JaneDoe649/PicoPAC/Kicad/PicoPAC.kicad_sch

## KiCad design Kicad/PicoPAC.kicad_sch (2024-10-13)

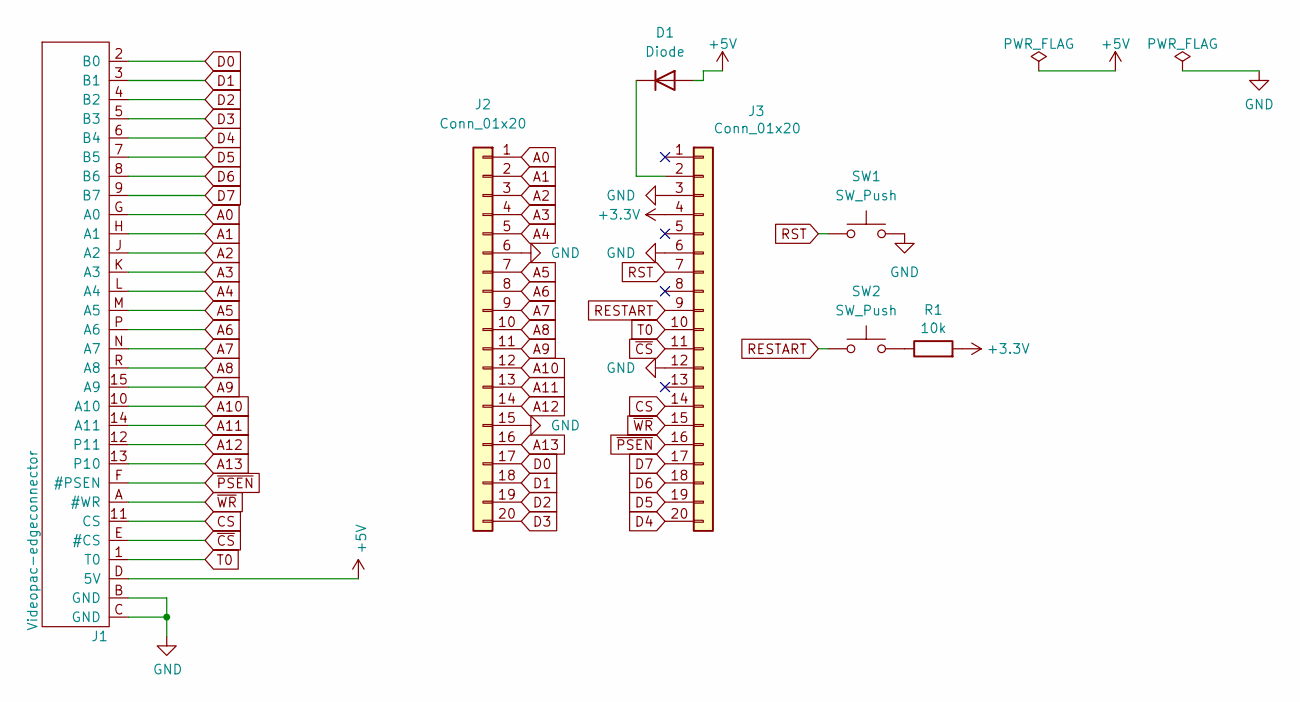
[picture p2: schematic PicoPAC.kicad_sch]

Parts:
D1: Diode; D_DO-35_SOD27_P7.62mm_Horizontal
J1: Videopac-edgeconnector; videopac-edgecon
J2, J3: Conn_01x20; PinSocket_1x20_P2.54mm_Vertical
R1: 10k; R_Axial_DIN0207_L6.3mm_D2.5mm_P7.62mm_Horizontal
SW1, SW2: SW_Push; SW_PUSH_6mm

Connections:
+3.3V: J3.4, R1.2
+5V: D1.2 (A), J1.D (5V)
A0: J1.G (A0), J2.1
A1: J1.H (A1), J2.2
A2: J1.J (A2), J2.3
A3: J1.K (A3), J2.4
A4: J1.L (A4), J2.5
A5: J1.M (A5), J2.7
A6: J1.P (A6), J2.8
A7: J1.N (A7), J2.9
A8: J1.R (A8), J2.10
A9: J1.15 (A9), J2.11
A10: J1.10 (A10), J2.12
A11: J1.14 (A11), J2.13
A12: J1.12 (P11), J2.14
A13: J1.13 (P10), J2.16
CS: J1.11 (CS), J3.14
D0: J1.2 (B0), J2.17
D1: J1.3 (B1), J2.18
D2: J1.4 (B2), J2.19
D3: J1.5 (B3), J2.20
D4: J1.6 (B4), J3.20
D5: J1.7 (B5), J3.19
D6: J1.8 (B6), J3.18
D7: J1.9 (B7), J3.17
GND: J1.B (GND), J1.C (GND), J2.6, J2.15, J3.3, J3.6, J3.12, SW1.2
unnamed: D1.1 (K), J3.2
unnamed: R1.1, SW2.2
RESTART: J3.9, SW2.1
RST: J3.7, SW1.1
T0: J1.1 (T0), J3.10
~CS: J1.E (#CS), J3.11
~PSEN: J1.F (#PSEN), J3.16
~WR: J1.A (#WR), J3.15
