JaneDoe649/PicoPAC/VSC-PicoPAC/selectgame.h

unsigned char __attribute__((aligned(4)))  selectgame[] = {0x44, 0xc3, 0x04, 0x09, 0x93, 0x00, 0x84, 0x0c, 0x84, 0x28, 0x04, 0x44, 0xa5, 0xb5, 0xb9, 0xa2, 0x81, 0xb8, 0x3f, 0x04, 0x30, 0x15, 0x99, 0xfe, 0x94, 0x28, 0x89, 0x03, 0x99, 0xfd, 0x94, 0x28, 0x99, 0xfc, 0x94, 0x28, 0x89, 0x03, 0x05, 0x83, 0xb9, 0x36, 0xf1, 0xd3, 0x12, 0x96, 0x32, 0xb4, 0x00, 0x83, 0xf1, 0xd3, 0x13, 0x96, 0x3a, 0xd4, 0x00, 0x83, 0xf1, 0xd3, 0x14, 0x96, 0x42, 0xf4, 0x00, 0x83, 0xf1, 0xd3, 0x15, 0x96, 0x4b, 0xf5, 0x14, 0x00, 0x83, 0xf1, 0xd3, 0x16, 0x96, 0x54, 0xf5, 0x34, 0x00, 0x83, 0xf1, 0xd3, 0x17, 0x96, 0x5d, 0xf5, 0x54, 0x00, 0x83, 0xf1, 0xd3, 0x18, 0x96, 0x66, 0xf5, 0x74, 0x00, 0x83, 0x83, 0xb8, 0x32, 0xb0, 0x01, 0x18, 0xb0, 0x23, 0x18, 0xb0, 0x45, 0x18, 0xb0, 0x67, 0x83, 0xfd, 0xe7, 0xe7, 0xad, 0x83, 0x94, 0x75, 0x91, 0x83, 0xff, 0xff, 0xff, 0xff, 0xff, 0xff, 0xff, 0xff, 0xff, 0xff, 0xff, 0xff, 0xff, 0xff, 0xff, 0xff, 0xff, 0xff, 0xff, 0xff, 0xff, 0xff, 0xff, 0xff, 0xff, 0xff, 0xff, 0xff, 0xff, 0xff, 0xff, 0xff, 0xff, 0xff, 0xff, 0xff, 0xff, 0xff, 0xff, 0xff, 0xff, 0xff, 0xff, 0xff, 0xff, 0xff, 0xff, 0xff, 0xff, 0xff, 0xff, 0xff, 0xff, 0xff, 0xff, 0xff, 0xff, 0xff, 0xff, 0xff, 0xff, 0xff, 0xff, 0xff, 0xff, 0xff, 0xff, 0xff, 0xff, 0xff, 0xff, 0xff, 0xff, 0xff, 0xff, 0xff, 0xff, 0xff, 0xff, 0xff, 0xff, 0xff, 0xff, 0xff, 0xff, 0xff, 0xff, 0xff, 0xff, 0xff, 0xff, 0xff, 0xff, 0xff, 0xff, 0xff, 0xff, 0xff, 0xff, 0xff, 0xff, 0xff, 0xff, 0xff, 0xff, 0xff, 0xff, 0xff, 0xff, 0xff, 0xff, 0xff, 0xff, 0xff, 0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
